adrirubio/tf-luna-security-system/firmware/S3-test/S3-test.ino

#include "esp_camera.h"
#include "FS.h"
#include "SPIFFS.h"

#include "board_config.h"

static bool save_one_photo(const char *path) {
  camera_fb_t *fb = esp_camera_fb_get();
  if (!fb) {
    Serial.println("Capture failed (fb is null)");
    return false;
  }

  File f = SPIFFS.open(path, FILE_WRITE);
  if (!f) {
    Serial.println("Failed to open file for writing");
    esp_camera_fb_return(fb);
    return false;
  }

  f.write(fb->buf, fb->len);
  f.close();
  esp_camera_fb_return(fb);

  Serial.printf("Saved %s (%u bytes)\n", path, fb->len);
  return true;
}

void setup() {
  Serial.begin(115200);
  delay(800);
  Serial.println("\nBoot: take one photo");

  // ----- SPIFFS -----
  if (!SPIFFS.begin(true)) {
    Serial.println("SPIFFS mount failed");
    while (true) delay(1000);
  }
  if (!SPIFFS.exists("/photos")) {
    SPIFFS.mkdir("/photos");
  }

  // ----- Camera config (S3-EYE pins come from camera_pins.h) -----
  camera_config_t config;
  config.ledc_channel = LEDC_CHANNEL_0;
  config.ledc_timer   = LEDC_TIMER_0;

  config.pin_d0 = Y2_GPIO_NUM;
  config.pin_d1 = Y3_GPIO_NUM;
  config.pin_d2 = Y4_GPIO_NUM;
  config.pin_d3 = Y5_GPIO_NUM;
  config.pin_d4 = Y6_GPIO_NUM;
  config.pin_d5 = Y7_GPIO_NUM;
  config.pin_d6 = Y8_GPIO_NUM;
  config.pin_d7 = Y9_GPIO_NUM;

  config.pin_xclk  = XCLK_GPIO_NUM;
  config.pin_pclk  = PCLK_GPIO_NUM;
  config.pin_vsync = VSYNC_GPIO_NUM;
  config.pin_href  = HREF_GPIO_NUM;

  config.pin_sccb_sda = SIOD_GPIO_NUM;
  config.pin_sccb_scl = SIOC_GPIO_NUM;

  config.pin_pwdn  = PWDN_GPIO_NUM;
  config.pin_reset = RESET_GPIO_NUM;

  config.xclk_freq_hz = 10000000;
  config.pixel_format = PIXFORMAT_JPEG;

  // Safe + small-ish so it’s reliable
  config.frame_size   = FRAMESIZE_VGA;   // 640x480
  config.jpeg_quality = 12;
  config.fb_count     = 1;
  config.grab_mode    = CAMERA_GRAB_WHEN_EMPTY;

  // Prefer PSRAM if present; otherwise DRAM
  if (psramFound()) {
    config.fb_location = CAMERA_FB_IN_PSRAM;
  } else {
    config.fb_location = CAMERA_FB_IN_DRAM;
  }

  // ----- Init camera -----
  esp_err_t err = esp_camera_init(&config);
  if (err != ESP_OK) {
    Serial.printf("Camera init failed: 0x%x\n", err);
    while (true) delay(1000);
  }

  // (Optional) If image is upside down on your unit, uncomment:
  // sensor_t *s = esp_camera_sensor_get();
  // s->set_vflip(s, 1);

  // ----- Take 1 photo -----
  const char *path = "/photos/boot.jpg";
  if (!save_one_photo(path)) {
    Serial.println("Failed to save photo");
  } else {
    Serial.println("Done.");
  }
}

void loop() {
  // nothing
  delay(1000);
}
